schnommus/formant_vco_prototype/vco_ltspice_tests/test_with.asc

A1: schmitt; VHigh=5 Vt=1.4 Vh=.45 Trise=.1u Tfall=.1u
C1: cap; 470p
D1: diode; 1N4148
D2: diode; 1N4148
I1: current; {ITUNE}
Q1: npn; BC547C
Q2: npn; BC547C
Q3: npn; BC547C
R1: res; 1K
R2: res; 10K
R3: res; 1K
R4: res; 10K
R5: res; 200
R6: res; 1K
U1: opamp
V3: voltage; 5
Named nets: 0
.tran 0 30m 0 startup
.lib opamp.sub
.param ITUNE=I
.step oct param ITUNE 0.1u 20u 1
