schnommus/formant_vco_prototype/vco_ltspice_tests/test_without.asc

A1: schmitt; VHigh=4 Vt=1.2 Vh=.4 Trise=.1u Tfall=.1u
C1: cap; 470p
I1: current; 5µ
Q3: npn; BC547C
R5: res; 200
R6: res; 2.5K
V3: voltage; 5
Named nets: 0
.tran 0 1m 0 startup
